rpd123/SCARA/stlfiles/arm-2_LONG.stl

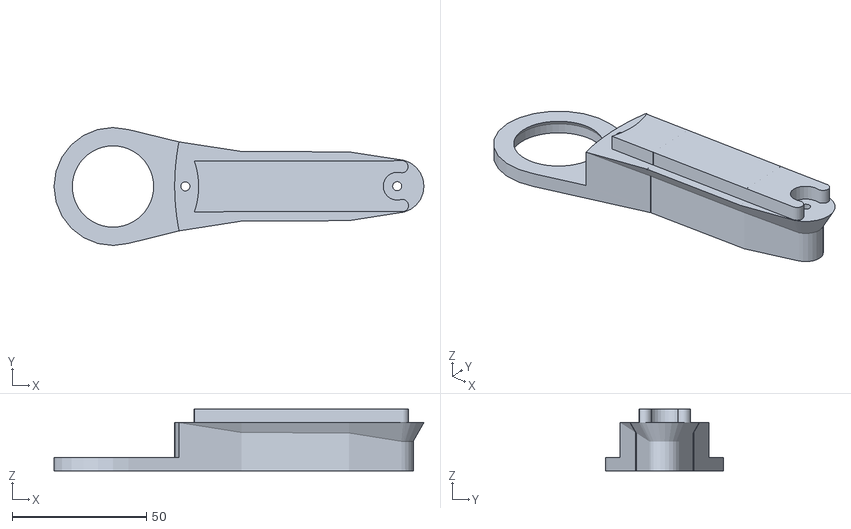
[picture p15: CAD file, 2022-07-06]
stlfiles/arm-2_LONG.stl
138.0 x 44.0 x 23.0
