rpd123/SCARA/Pybot stlfiles/not wanted/lsshank1.stl

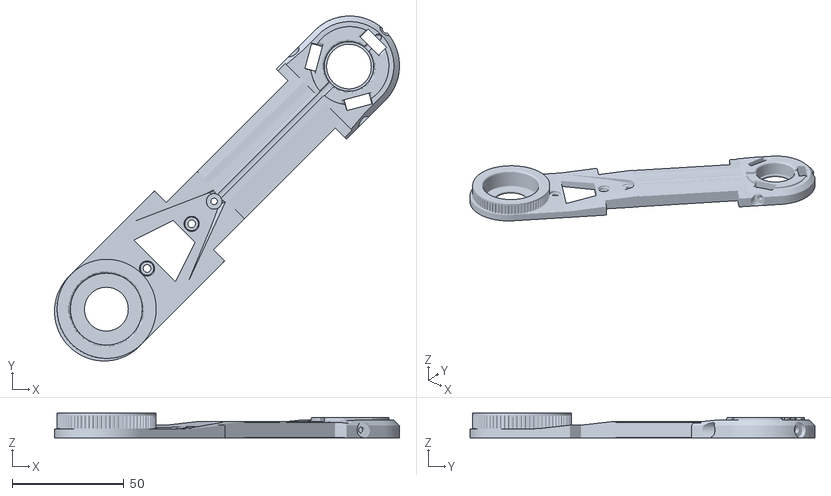
[picture p16: CAD file, 2022-08-31]
Pybot stlfiles/not wanted/lsshank1.stl
154.4 x 154.4 x 11.0
