rpd123/SCARA/Pybot stlfiles/REDUCTION_[V10 (1).stl

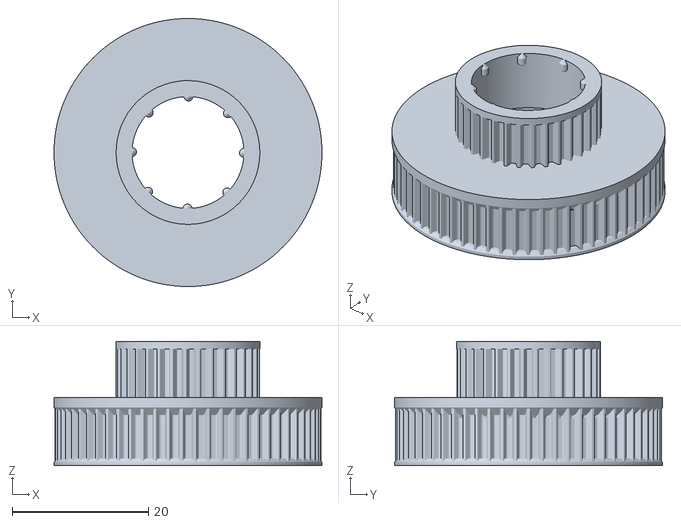
[picture p17: CAD file, 2022-08-10]
Pybot stlfiles/REDUCTION_[V10 (1).stl
39.3 x 39.3 x 18.2
