rpd123/SCARA/stlfiles/3fingergripper/GripperFinger.stl

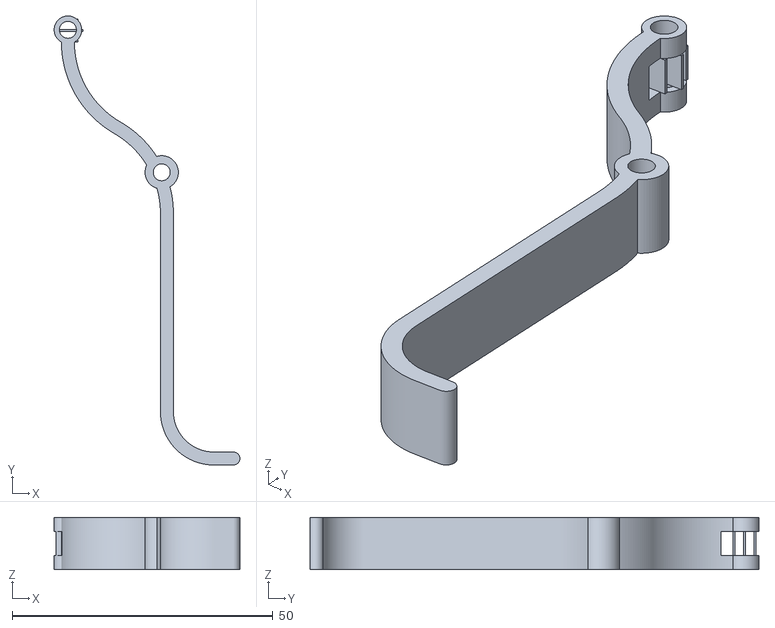
[picture p18: CAD file, 2022-07-06]
stlfiles/3fingergripper/GripperFinger.stl
35.6 x 86.2 x 10.0
