rpd123/SCARA/stlfiles/gt2-62-13-32.stl

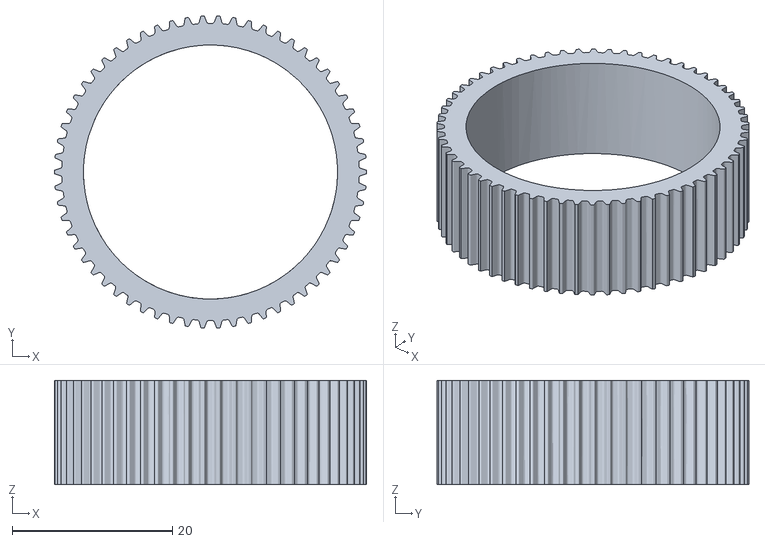
[picture p19: CAD file, 2022-07-06]
stlfiles/gt2-62-13-32.stl
39.0 x 39.0 x 13.0
