rpd123/SCARA/Pybot stlfiles/not wanted/ARM_TOP_[V9.stl

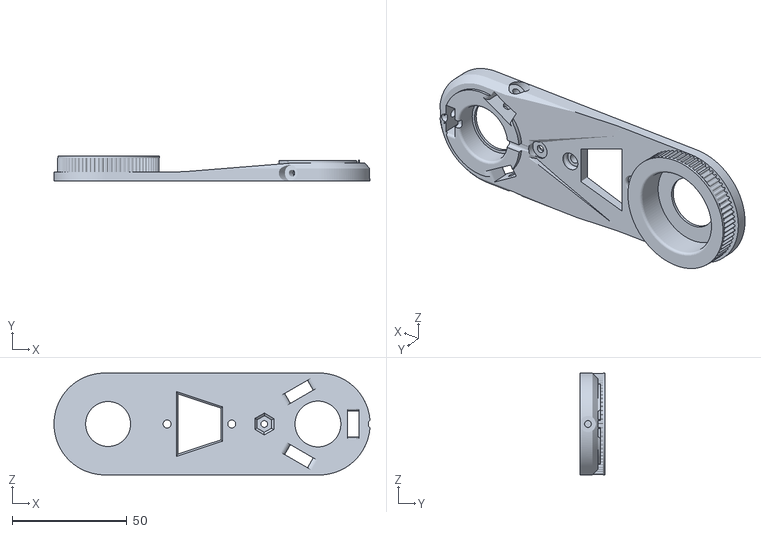
[picture p20: CAD file, 2022-08-10]
Pybot stlfiles/not wanted/ARM_TOP_[V9.stl
137.9 x 11.0 x 44.5
