rpd123/SCARA/Pybot stlfiles/Z_BASE_[V10.stl

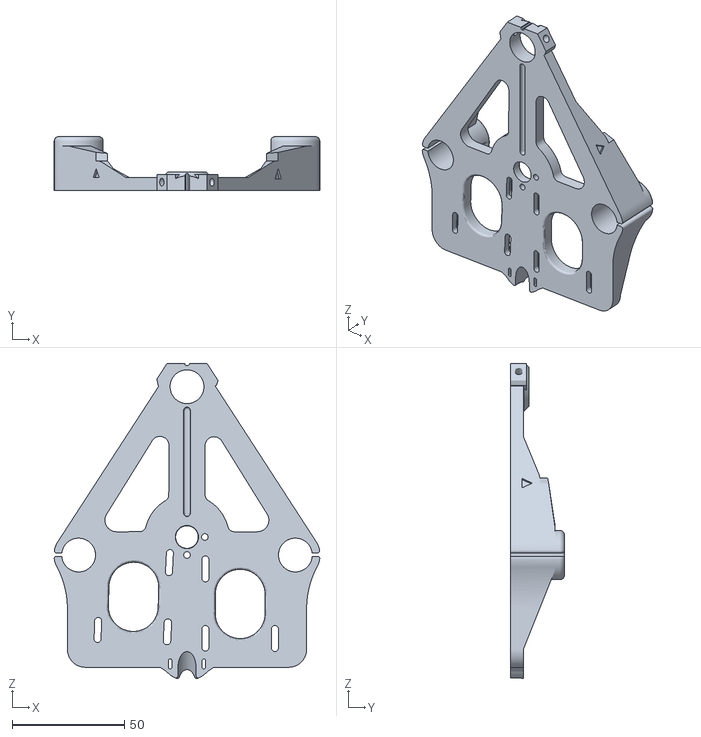
[picture p21: CAD file, 2022-08-10]
Pybot stlfiles/Z_BASE_[V10.stl
118.4 x 24.0 x 140.4
