rpd123/SCARA/stlfiles/3fingergripper/GripperServoDisk.stl

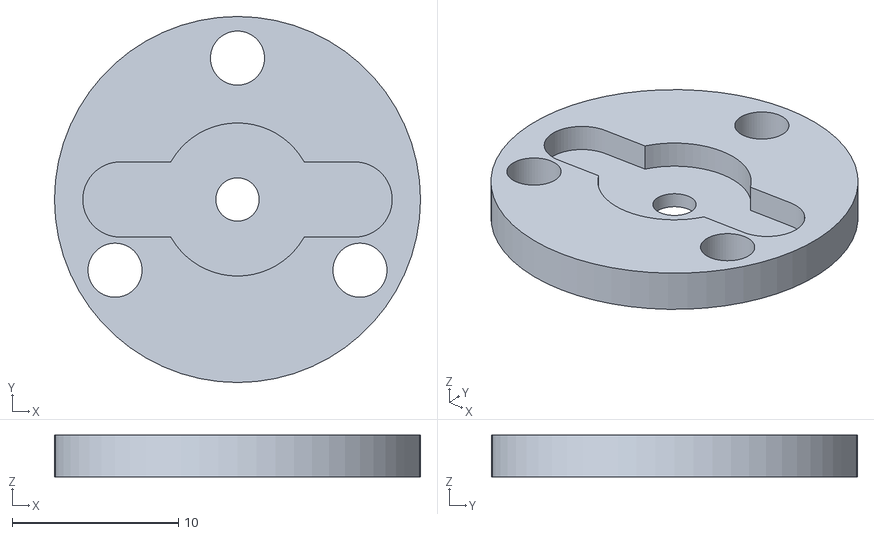
[picture p22: CAD file, 2022-07-06]
stlfiles/3fingergripper/GripperServoDisk.stl
22.0 x 22.0 x 2.50
