rpd123/SCARA/stlfiles/top.stl

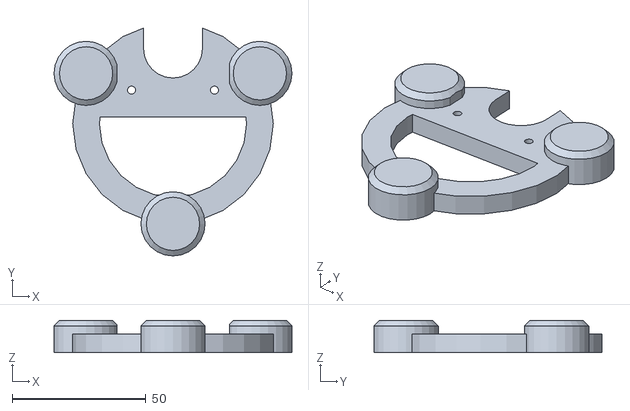
[picture p23: CAD file, 2022-07-06]
stlfiles/top.stl
89.0 x 85.2 x 12.0
