rpd123/SCARA/Pybot stlfiles/CAP_[V10.stl

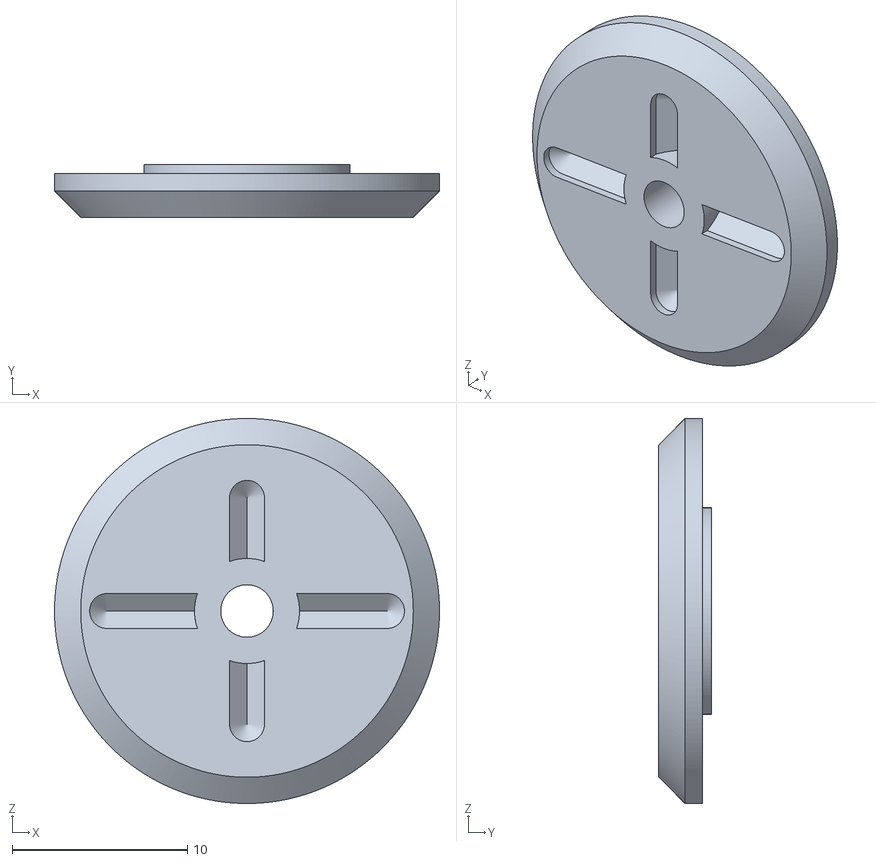
[picture p24: CAD file, 2022-08-10]
Pybot stlfiles/CAP_[V10.stl
22.0 x 3.00 x 22.0
