rpd123/SCARA/Pybot stlfiles/not wanted/electronics_case.stl

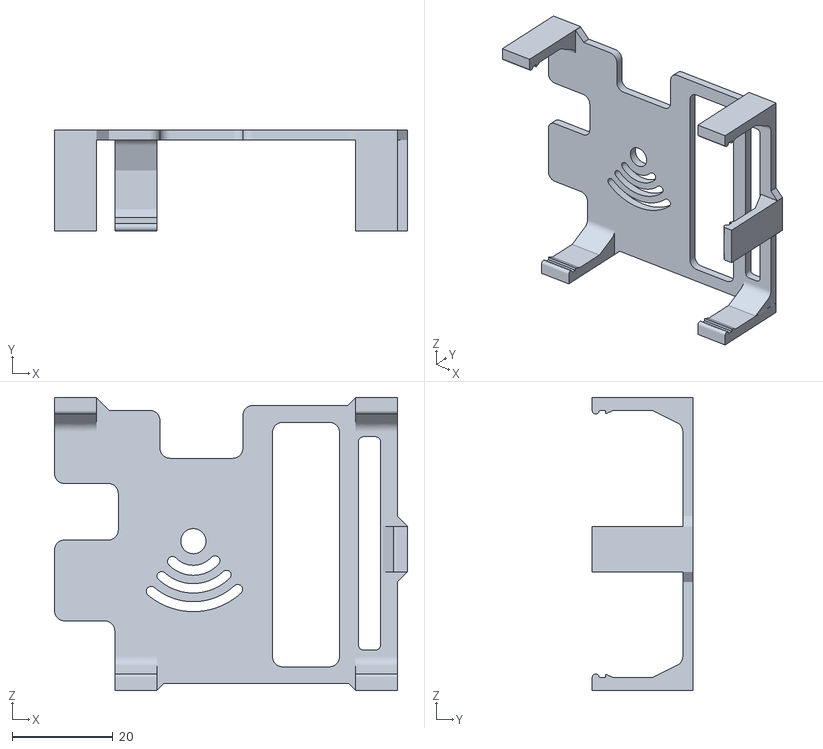
[picture p25: CAD file, 2022-08-10]
Pybot stlfiles/not wanted/electronics_case.stl
70.1 x 20.0 x 58.2
