rpd123/SCARA/stlfiles/motor-bearing-bottom.stl

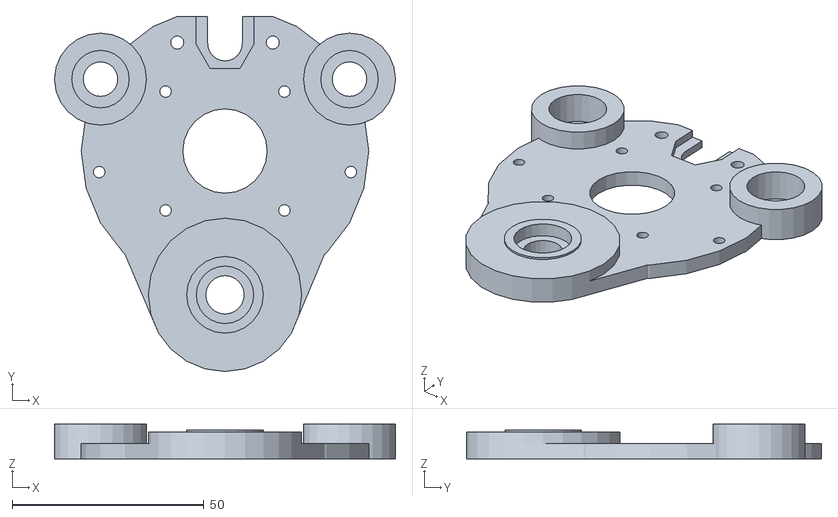
[picture p26: CAD file, 2022-07-06]
stlfiles/motor-bearing-bottom.stl
89.0 x 92.6 x 9.00
