rpd123/SCARA/Pybot stlfiles/not wanted/GRIPPER-_NAILS_[V10.stl

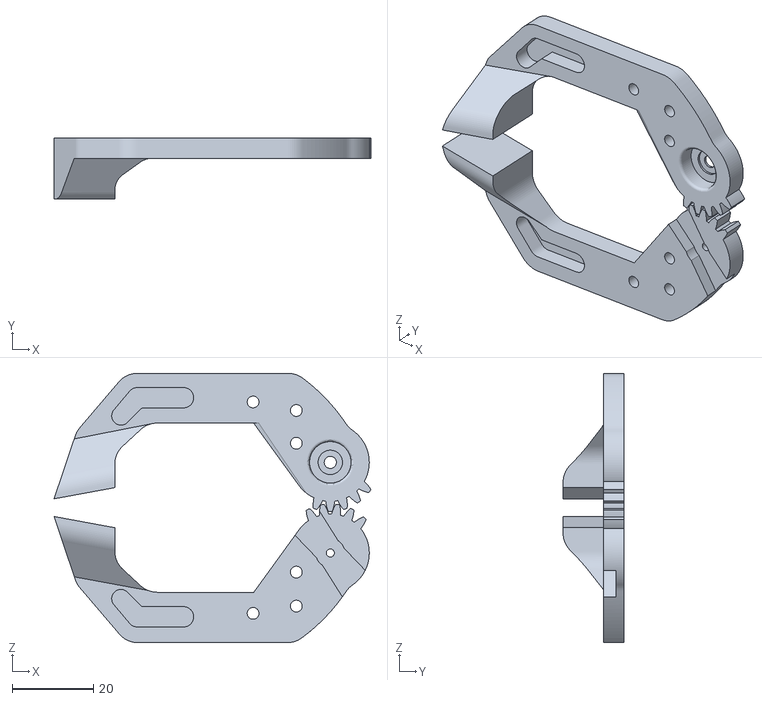
[picture p27: CAD file, 2022-08-10]
Pybot stlfiles/not wanted/GRIPPER-_NAILS_[V10.stl
78.0 x 15.0 x 66.3
