rpd123/SCARA/Pybot stlfiles/TOP_TRIANGLE_[V10.stl

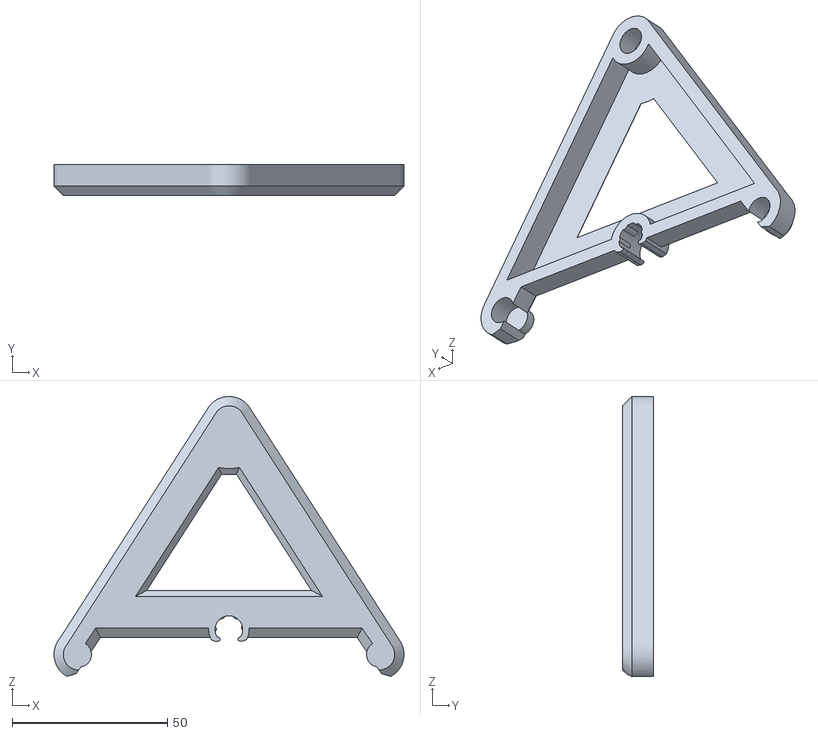
[picture p28: CAD file, 2022-08-10]
Pybot stlfiles/TOP_TRIANGLE_[V10.stl
112.6 x 10.0 x 90.1
