rpd123/SCARA/stlfiles/arm-1_LONG.stl

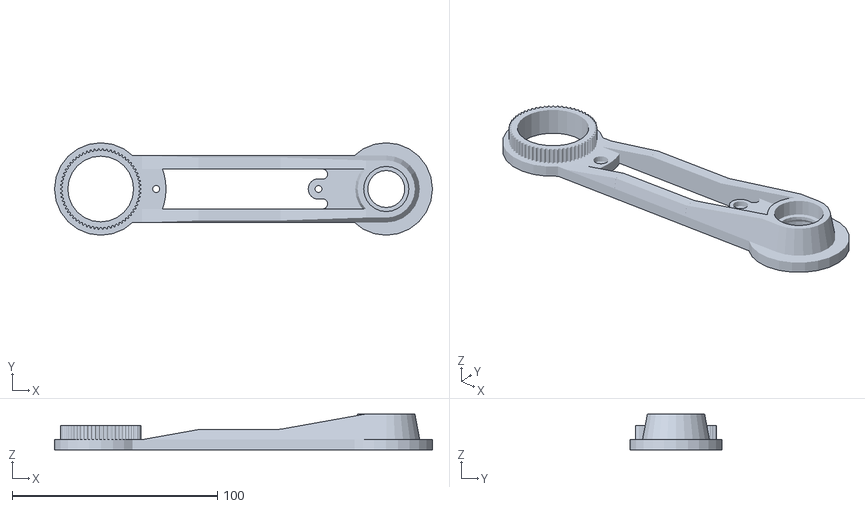
[picture p29: CAD file, 2022-07-06]
stlfiles/arm-1_LONG.stl
184.0 x 45.0 x 17.5
