rpd123/SCARA/Pybot stlfiles/longbottomshank1.stl

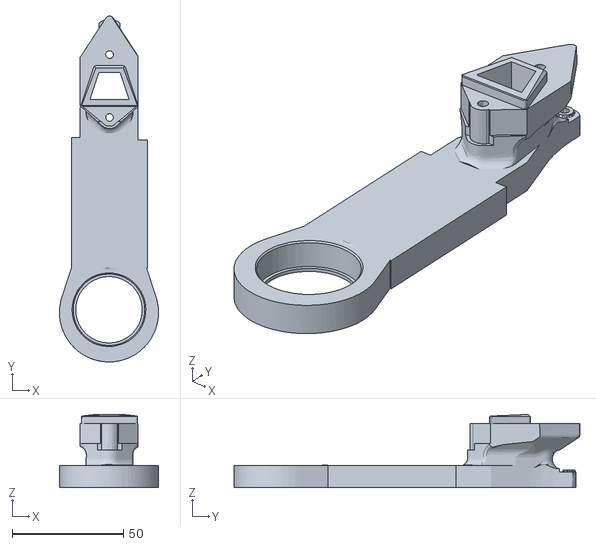
[picture p30: CAD file, 2022-08-10]
Pybot stlfiles/longbottomshank1.stl
44.5 x 155.3 x 32.8
