rpd123/SCARA/Pybot stlfiles/not wanted/ARM_BOTTOM_[V10.stl

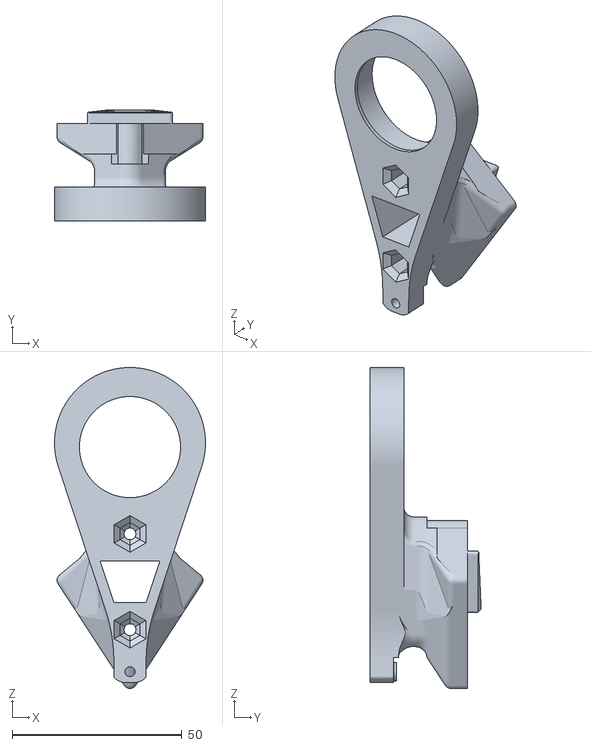
[picture p31: CAD file, 2022-08-10]
Pybot stlfiles/not wanted/ARM_BOTTOM_[V10.stl
44.5 x 32.8 x 94.6
