rpd123/SCARA/stlfiles/arm-1.stl

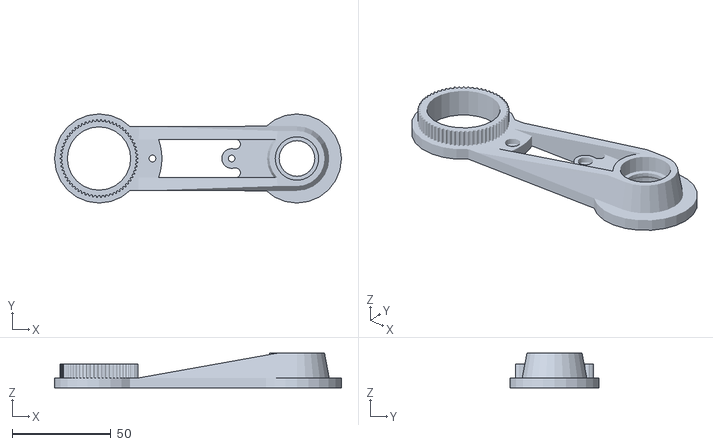
[picture p32: CAD file, 2022-07-06]
stlfiles/arm-1.stl
145.0 x 45.0 x 17.5
