rpd123/SCARA/Pybot stlfiles/CABLES_CAP_[V10.stl

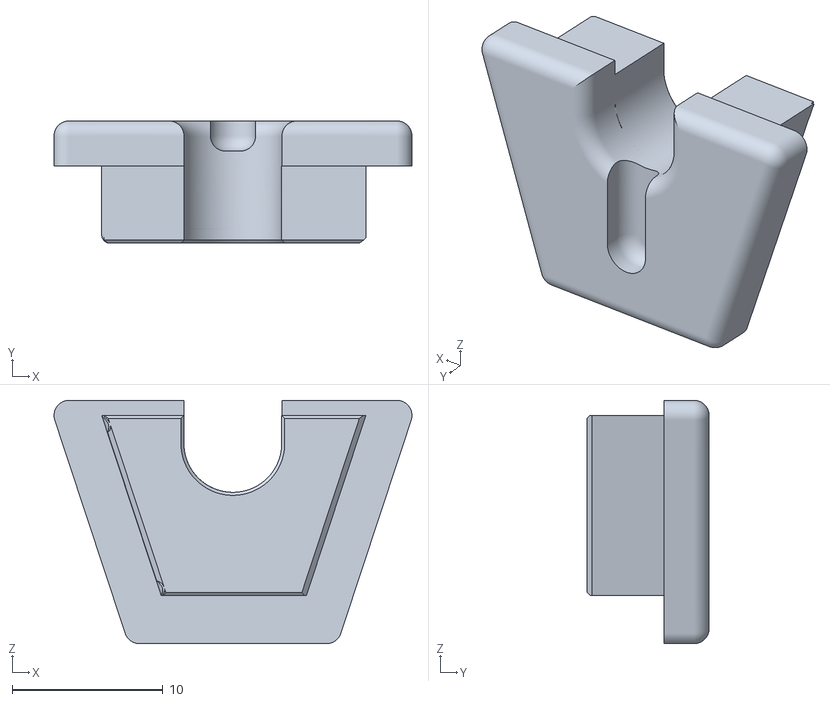
[picture p33: CAD file, 2022-08-10]
Pybot stlfiles/CABLES_CAP_[V10.stl
23.7 x 8.10 x 16.1
