rpd123/SCARA/Pybot stlfiles/not wanted/LEFT_and_RIGHT_nails_SEPARATED_V3.stl

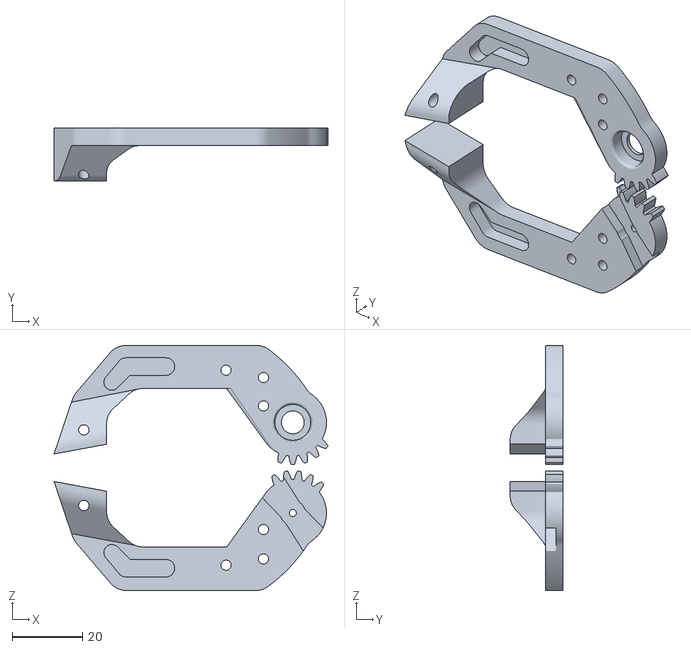
[picture p34: CAD file, 2022-08-10]
Pybot stlfiles/not wanted/LEFT_and_RIGHT_nails_SEPARATED_V3.stl
78.0 x 15.0 x 69.8
