rpd123/SCARA/stlfiles/bottom.stl

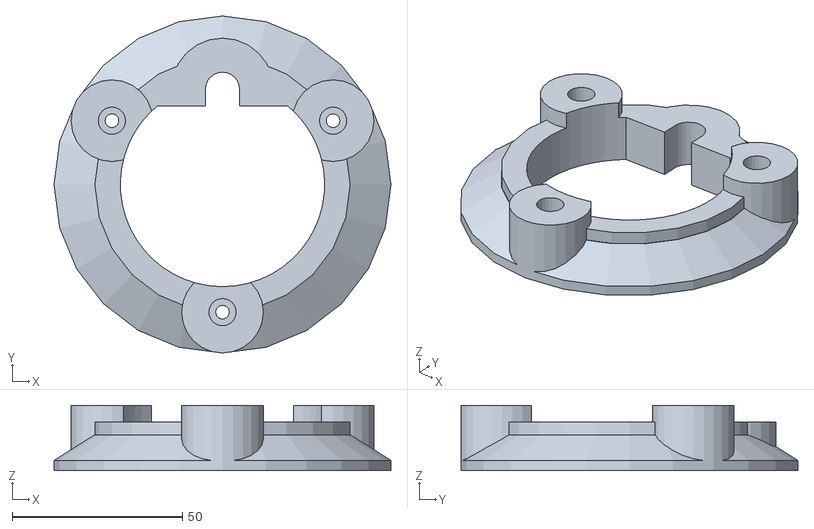
[picture p35: CAD file, 2022-07-06]
stlfiles/bottom.stl
99.0 x 99.0 x 19.2
