rpd123/SCARA/Pybot stlfiles/not wanted/FOREAM_[V10.stl

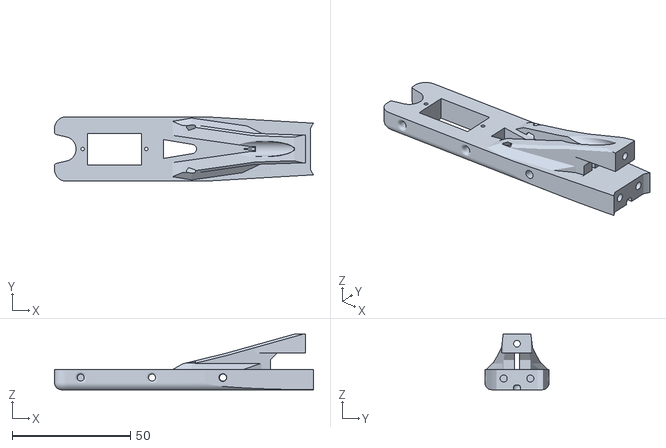
[picture p36: CAD file, 2022-08-10]
Pybot stlfiles/not wanted/FOREAM_[V10.stl
109.6 x 27.2 x 23.5
