rpd123/SCARA/stlfiles/motor-bearing-top.stl

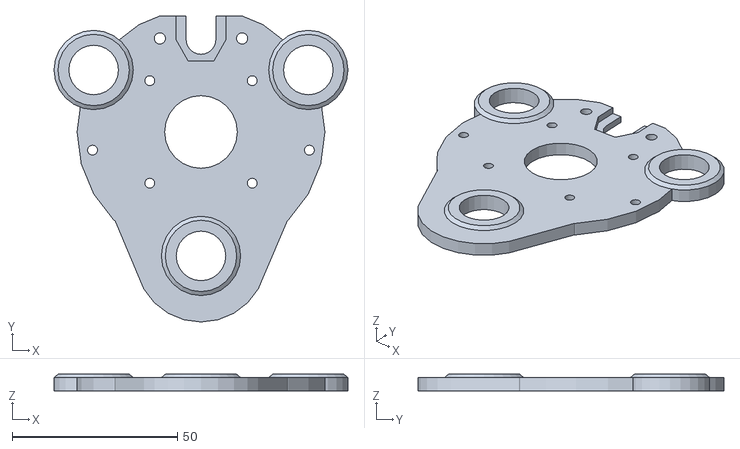
[picture p37: CAD file, 2022-07-06]
stlfiles/motor-bearing-top.stl
89.0 x 92.6 x 5.00
