rpd123/SCARA/Pybot stlfiles/not wanted/Gripper holder.stl

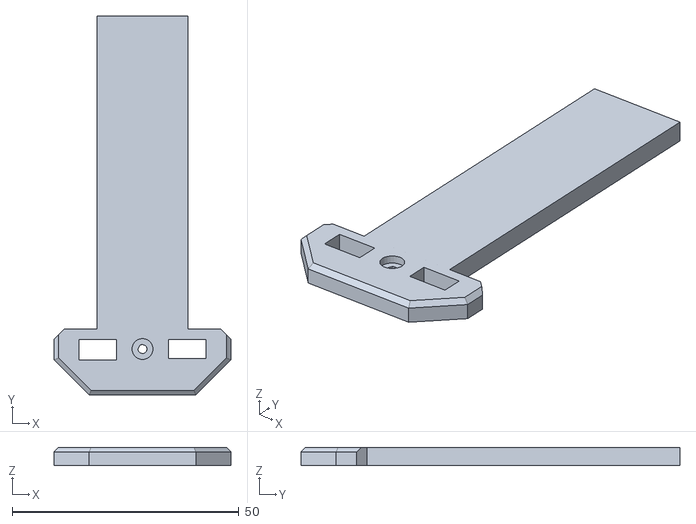
[picture p38: CAD file, 2022-08-10]
Pybot stlfiles/not wanted/Gripper holder.stl
39.0 x 83.5 x 4.00
