rpd123/SCARA/stlfiles/arm-3.stl

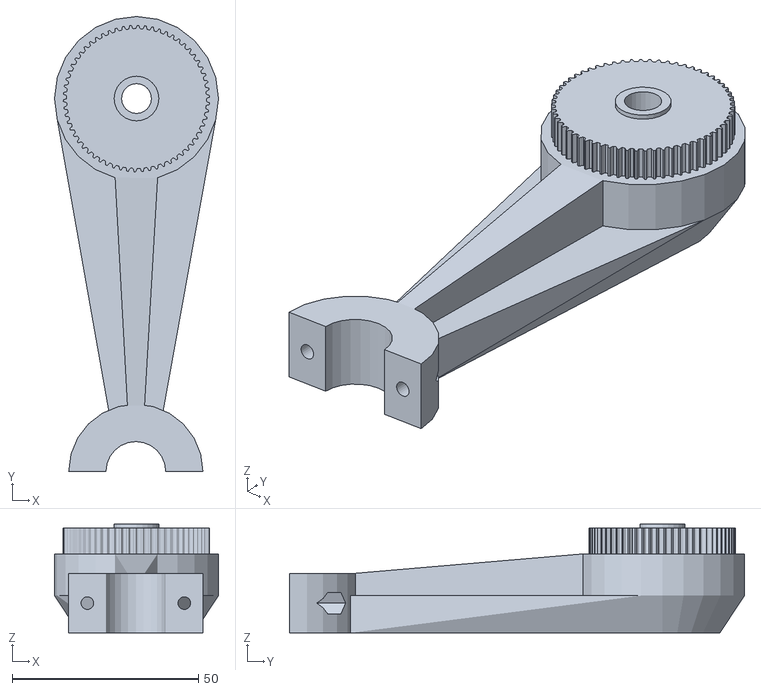
[picture p39: CAD file, 2022-07-06]
stlfiles/arm-3.stl
44.0 x 122.0 x 29.2
