rpd123/SCARA/Pybot stlfiles/not wanted/long arm bottom.stl

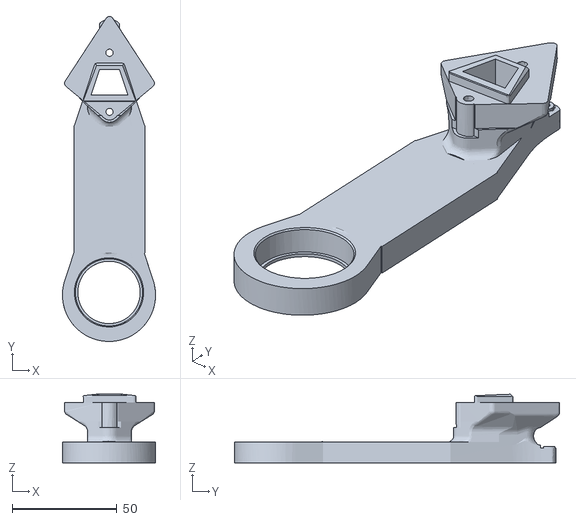
[picture p40: CAD file, 2022-08-10]
Pybot stlfiles/not wanted/long arm bottom.stl
44.5 x 155.3 x 32.8
