rpd123/SCARA/stlfiles/arm-2.stl

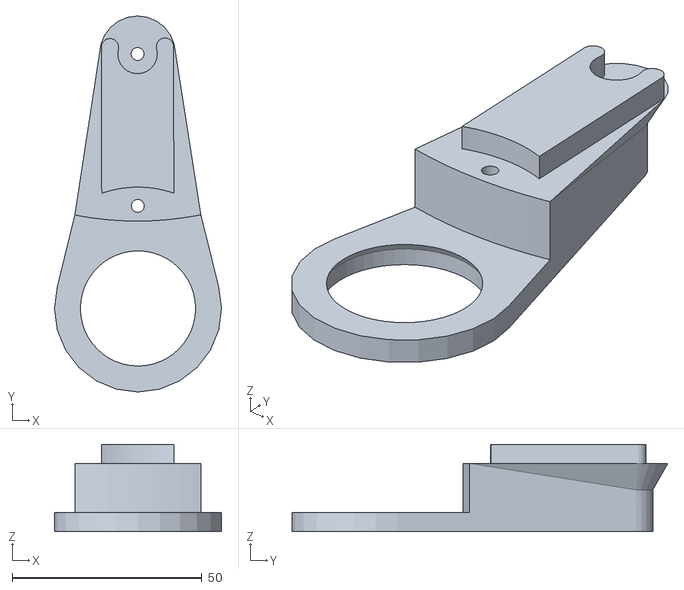
[picture p41: CAD file, 2022-07-06]
stlfiles/arm-2.stl
44.0 x 99.0 x 23.0
