rpd123/SCARA/Pybot stlfiles/not wanted/ARM_HUB_[V11.stl

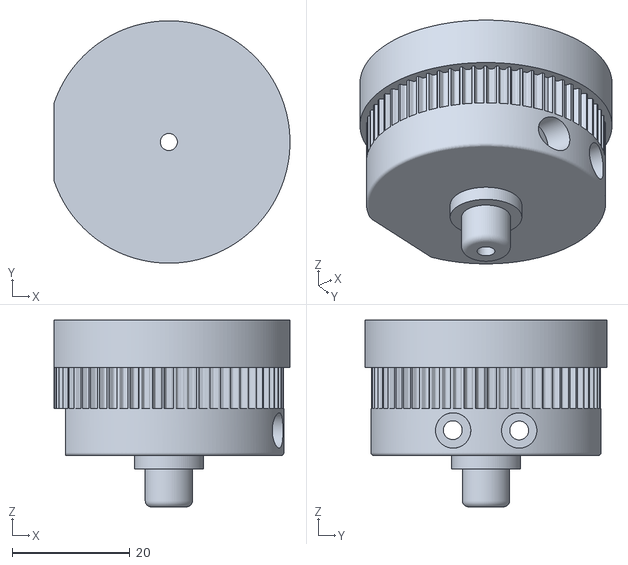
[picture p42: CAD file, 2022-08-10]
Pybot stlfiles/not wanted/ARM_HUB_[V11.stl
40.1 x 41.2 x 31.7
