rpd123/SCARA/stlfiles/spacer.stl

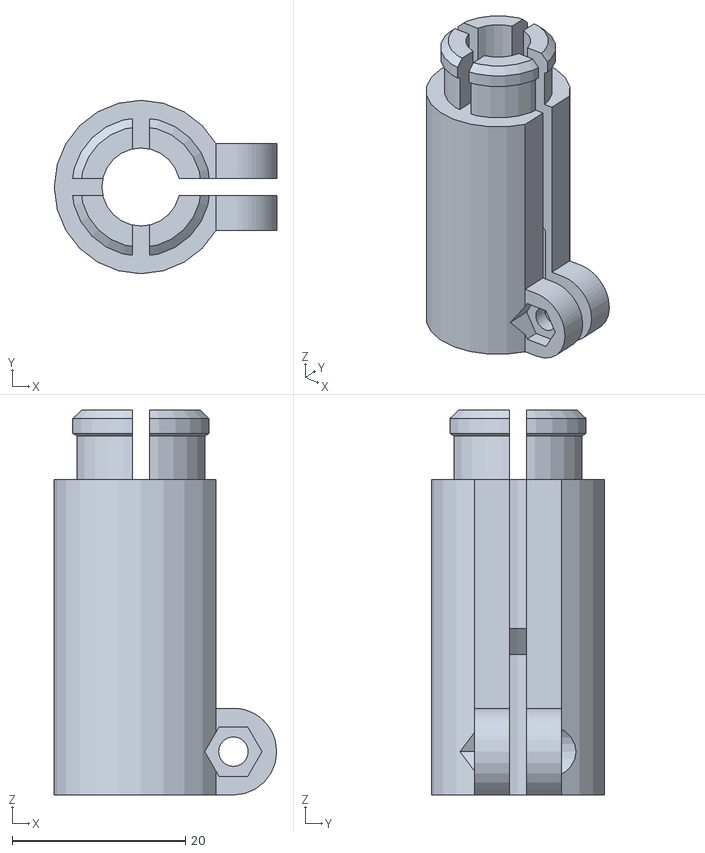
[picture p43: CAD file, 2022-07-06]
stlfiles/spacer.stl
25.7 x 20.0 x 44.4
