rpd123/SCARA/Pybot stlfiles/not wanted/GRIPPER-_BASE_[V10.stl

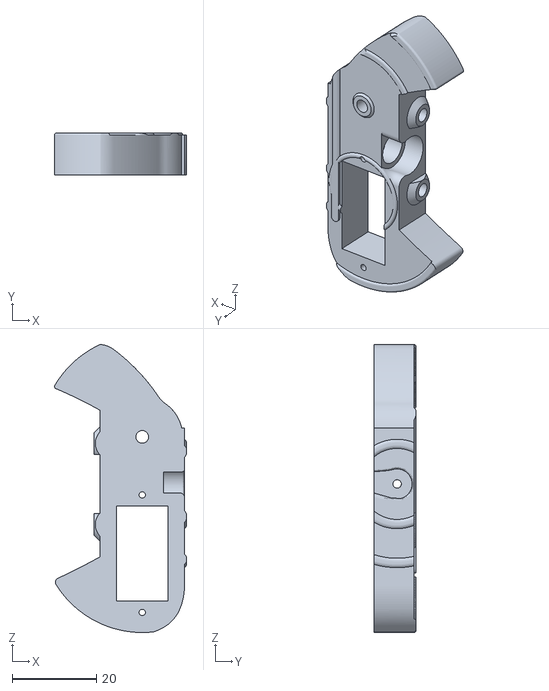
[picture p44: CAD file, 2022-08-10]
Pybot stlfiles/not wanted/GRIPPER-_BASE_[V10.stl
31.3 x 10.0 x 68.2
