rpd123/SCARA/stlfiles/arm-4.stl

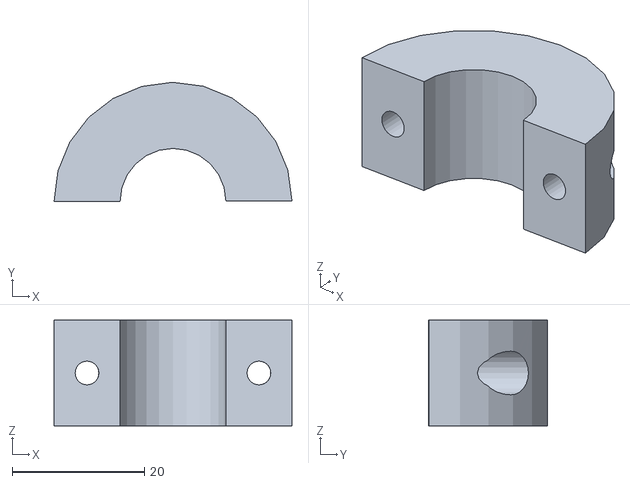
[picture p45: CAD file, 2022-07-06]
stlfiles/arm-4.stl
36.0 x 18.1 x 16.0
