rpd123/SCARA/Pybot stlfiles/not wanted/PEN_HOLDER_[V10.stl

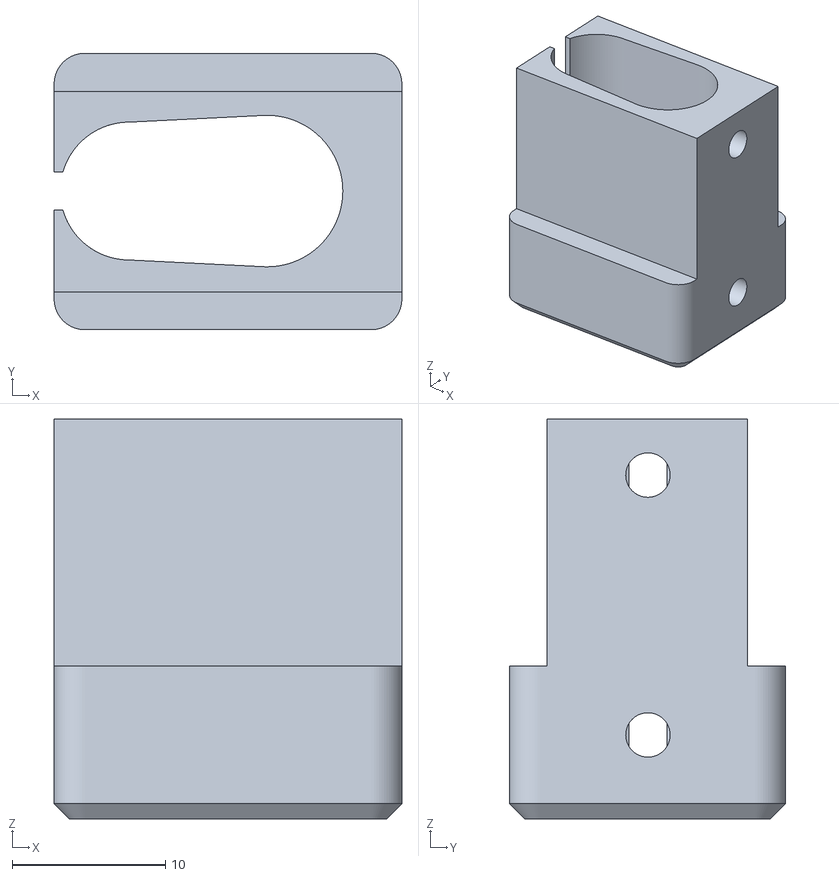
[picture p46: CAD file, 2022-08-10]
Pybot stlfiles/not wanted/PEN_HOLDER_[V10.stl
22.7 x 18.0 x 26.1
