rpd123/SCARA/stlfiles/nutholder.stl

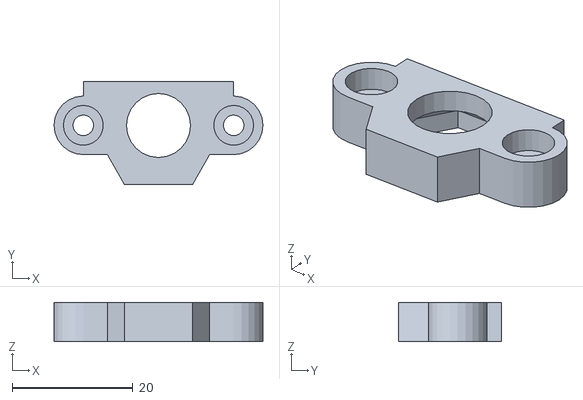
[picture p47: CAD file, 2022-07-06]
stlfiles/nutholder.stl
34.6 x 17.0 x 6.50
