rpd123/SCARA/Pybot stlfiles/not wanted/Mod forearm.stl

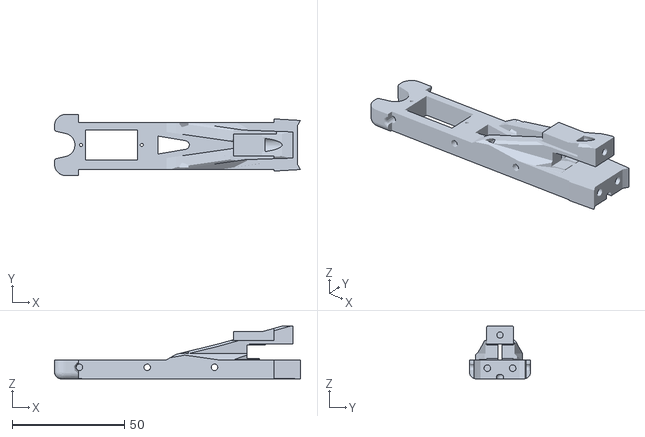
[picture p48: CAD file, 2022-08-10]
Pybot stlfiles/not wanted/Mod forearm.stl
109.6 x 27.2 x 23.5
